palazzol/demon/targets/bin/asteroid_tether/asteroid_tether.rst

                              1 ;****************************************************************
                              2 ; This file is auto-generated by ddmake from asteroid_tether.toml
                              3 ; *** DO NOT EDIT ***
                              4 ;****************************************************************
                              5 
                              6 ; Start of chip memory mapping
                     F800     7 STRTADD = 0xf800
                              8 
                              9 ; 2K ROM
                     0800    10 ROMSIZE = 0x0800
                             11 
                             12 ; Start of ram, needs 7 bytes starting here
                             13 ; On the 6502, you can usually you can count on there being RAM in page 0
                     0000    14 RAMSTRT = 0x0000
                             15 
                             16 ; Start of stack, needs some memory below this address
                             17 ; On the 6502, this is in page 1, so this actually represents
                             18 ; address 0x0100+SSTACK
                     00FF    19 SSTACK = 0x00ff
                             20 
                             21 ; delay factor
                     0180    22 BIGDEL = 0x0180
                             23 
                             24         .include "../core/dd.def"
                              1 
                     0000     2 ROMEND  .equ    STRTADD+ROMSIZE
                              3 
                              4 
                             25         .include "../core/6502.def"
                              1 ; Same for all 6502s
                     FFFA     2 VECTORS .equ    0xfffa      ; location of Vector table
                             26 
                             27 ;------- region1  -----------------------------------------------
                             28 
                             29         .bank   region1 (base=STRTADD, size=VECTORS-STRTADD)
                             30         .area   region1 (ABS, BANK=region1)
                             31 
                             32 ;
                             33 ;       START CODE
                             34 ;
   F800                      35 START:
   F800 78            [ 2]   36         sei              ; Disable interrupts - we don't handle them
   F801 A2 FF         [ 2]   37         ldx     #SSTACK  ; set up the stack
   F803 9A            [ 2]   38         txs
   F804 D8            [ 2]   39         cld              ; No Decimal
                             40 ;       YOUR CODE CAN GO HERE
   F805 4C 08 F8      [ 3]   41         jmp     INIT
                             42 
                             43         .include "../core/6502_main.asm"
                              1 ;;;;;;;;;;;;;;;;;;;;;;;;;;;;;;;;;;;;;;;;;;;;;;;;;;;;;;;;;;;;;;;;;;;;;;;;;;;
                              2 ; RAM Variables 
                              3 ;;;;;;;;;;;;;;;;;;;;;;;;;;;;;;;;;;;;;;;;;;;;;;;;;;;;;;;;;;;;;;;;;;;;;;;;;;;
                              4 
                     0000     5 OUTBUF  .equ    RAMSTRT         ;buffer for output states
                     0001     6 B       .equ    RAMSTRT+0x01    ;general purpose
                     0002     7 C       .equ    RAMSTRT+0x02    ;general purpose
                     0003     8 CMDBUF0 .equ    RAMSTRT+0x03    ;command buffer
                     0004     9 CMDBUF1 .equ    RAMSTRT+0x04    ;command buffer
                     0005    10 CMDBUF2 .equ    RAMSTRT+0x05    ;command buffer
                     0006    11 CMDBUF3 .equ    RAMSTRT+0x06    ;command buffer
                             12 
                             13 ; I2C ADDRESSING
                     0011    14 I2CRADR .equ    0x11        ; I2C read address  - I2C address 0x08
                     0010    15 I2CWADR .equ    0x10        ; I2C write address - I2C address 0x08
                             16 
   F808                      17 INIT:
   F808 A9 00         [ 2]   18         lda     #0x00
   F80A 85 00         [ 3]   19         sta     OUTBUF
                             20 
                             21 ; Main routine
   F80C                      22 MAIN:
   F80C 20 0B F9      [ 6]   23         jsr     EVERY
   F80F 20 C6 F8      [ 6]   24         jsr     POLL
   F812 B0 F8         [ 4]   25         bcs     MAIN
   F814 A9 01         [ 2]   26         lda     #BIGDEL>>8
   F816 85 01         [ 3]   27         sta     B
   F818 A9 80         [ 2]   28         lda     #BIGDEL%256
   F81A 85 02         [ 3]   29         sta     C
   F81C                      30 MLOOP:
   F81C A5 02         [ 3]   31         lda     C
   F81E F0 05         [ 4]   32         beq     DECBOTH
   F820 C6 02         [ 5]   33         dec     C
   F822 4C 1C F8      [ 3]   34         jmp     MLOOP
   F825                      35 DECBOTH:
   F825 A5 01         [ 3]   36         lda     B
   F827 F0 E3         [ 4]   37         beq     MAIN
   F829 C6 02         [ 5]   38         dec     C
   F82B C6 01         [ 5]   39         dec     B
   F82D 4C 1C F8      [ 3]   40         jmp     MLOOP
                             41 
                             42 ; Delay for half a bit time
   F830 60            [ 6]   43 I2CDLY: rts             ; TBD - this is plenty?
                             44 
                             45 ; I2C Start Condition
   F831                      46 I2CSTART:
   F831 20 30 F9      [ 6]   47         jsr    CLRSDA      
   F834 20 19 F9      [ 6]   48         jsr    CLRSCL
   F837 60            [ 6]   49         rts
                             50 
                             51 ; I2C Stop Condition
                             52 ; Uses HL
                             53 ; Destroys A
   F838                      54 I2CSTOP:
   F838 20 30 F9      [ 6]   55         jsr    CLRSDA
   F83B 20 0C F9      [ 6]   56         jsr    SETSCL
   F83E 20 23 F9      [ 6]   57         jsr    SETSDA
   F841 60            [ 6]   58         rts
                             59         
   F842                      60 I2CRBIT:
   F842 20 23 F9      [ 6]   61         jsr     SETSDA
   F845 20 0C F9      [ 6]   62         jsr     SETSCL
   F848 20 3D F9      [ 6]   63         jsr     READSDA ; sets/clears carry flag
   F84B 20 19 F9      [ 6]   64         jsr     CLRSCL
   F84E 60            [ 6]   65         rts             ; carry flag still good here
                             66 
   F84F                      67 I2CWBIT:
   F84F 90 06         [ 4]   68         bcc     DOCLR
   F851 20 23 F9      [ 6]   69         jsr     SETSDA
   F854 4C 5A F8      [ 3]   70         jmp     AHEAD
   F857                      71 DOCLR:
   F857 20 30 F9      [ 6]   72         jsr     CLRSDA
   F85A                      73 AHEAD:
   F85A 20 0C F9      [ 6]   74         jsr     SETSCL
   F85D 20 19 F9      [ 6]   75         jsr     CLRSCL
   F860 60            [ 6]   76         rts
                             77         
   F861                      78 I2CWBYTE:
   F861 48            [ 3]   79         pha
   F862 A9 08         [ 2]   80         lda     #0x08
   F864 85 01         [ 3]   81         sta     B
   F866 68            [ 4]   82         pla
   F867                      83 ILOOP:
   F867 2A            [ 2]   84         rol
   F868 48            [ 3]   85         pha
   F869 20 4F F8      [ 6]   86         jsr     I2CWBIT
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
   F8F1 A5 05         [ 3]  164         lda     CMDBUF2
   F8F3 85 01         [ 3]  165         sta     B
   F8F5 A5 04         [ 3]  166         lda     CMDBUF1
   F8F7 85 02         [ 3]  167         sta     C
   F8F9 60            [ 6]  168         rts
                            169         
   F8FA                     170 SRESP:
   F8FA 20 B5 F8      [ 6]  171         jsr    I2CSRESP
   F8FD                     172 RHERE:
   F8FD 38            [ 2]  173         sec
   F8FE 60            [ 6]  174         rts
   F8FF                     175 REMCALL:
   F8FF A9 F7         [ 2]  176         lda     #>(START-1)
   F901 48            [ 3]  177         pha
   F902 A9 FF         [ 2]  178         lda     #<(START-1)
   F904 48            [ 3]  179         pha
   F905 20 F1 F8      [ 6]  180         jsr     LOADBC
   F908 6C 01 00      [ 5]  181         jmp     [B]
                            182         
                            183 ;;;;;;;;;;
                            184 
                            185 
                             44 ;
                             45 ;       EVERY CODE
                             46 ;
   F90B                      47 EVERY:
                             48 ;       YOUR CODE CAN GO HERE
   F90B 60            [ 6]   49         rts
                             50 
                             51         .include "../io/asteroid-tether.asm"
                              1 
                              2 ; SCL  - WRITE 0x3200, bit0 (0x01) 2 player start lamp - active low only because led is wired to +5V
                              3 ; DOUT - WRITE 0x3200, bit1 (0x02) 1 player start lamp - active low only because led is wired to +5V
                              4 ; DIN  - READ  0x2405, bit7 (0x80) thrust button - inverted on input
                              5 
                     2800     6 DIP7    .equ    0x2800  ;bit0 = DIP switch 7
                     3200     7 LEDS    .equ    0x3200  ;bit0 = 2 player start lamp
                              8                         ;bit1 = 1 player start lamp
                              9         
                     0000    10 LEDBUF  .equ    OUTBUF  ;buffer for lamps
                             11 
   F90C A5 00         [ 3]   12 SETSCL: lda     LEDBUF
   F90E 09 01         [ 2]   13         ora     #0x01
   F910 85 00         [ 3]   14         sta     LEDBUF
   F912 8D 00 32      [ 4]   15         sta     LEDS
   F915 20 30 F8      [ 6]   16         jsr     I2CDLY
   F918 60            [ 6]   17         rts
                             18 
   F919 A5 00         [ 3]   19 CLRSCL: lda     LEDBUF
   F91B 29 FE         [ 2]   20         and     #0xfe
   F91D 85 00         [ 3]   21         sta     LEDBUF
   F91F 8D 00 32      [ 4]   22         sta     LEDS
   F922 60            [ 6]   23         rts
                             24     
   F923 A5 00         [ 3]   25 SETSDA: lda     LEDBUF
   F925 29 FD         [ 2]   26         and     #0xfd
   F927 85 00         [ 3]   27         sta     LEDBUF
   F929 8D 00 32      [ 4]   28         sta     LEDS
   F92C 20 30 F8      [ 6]   29         jsr     I2CDLY
   F92F 60            [ 6]   30         rts
                             31 
   F930 A5 00         [ 3]   32 CLRSDA: lda     LEDBUF
   F932 09 02         [ 2]   33         ora     #0x02
   F934 85 00         [ 3]   34         sta     LEDBUF
   F936 8D 00 32      [ 4]   35         sta     LEDS
   F939 20 30 F8      [ 6]   36         jsr     I2CDLY
   F93C 60            [ 6]   37         rts
                             38 
   F93D                      39 READSDA:        
   F93D AD 00 28      [ 4]   40         lda DIP7
   F940 6A            [ 2]   41         ror         
   F941 60            [ 6]   42         rts
                             43      
                             44     
                             52 ;
                             53 ;       NMI HANDLER
                             54 ;
   F942                      55 NMI:
   F942 40            [ 6]   56         rti
                             57 
                             58 
                             59 ;------- region2  -----------------------------------------------
                             60 
                             61         .bank   region2 (base=VECTORS, size=ROMSIZE-VECTORS)
                             62         .area   region2 (ABS, BANK=region2)
                             63 
                             64         .include "../core/6502_vectors.asm"
   FFFA 42 F9                 1         .dw     NMI
   FFFC 00 F8                 2         .dw     START
   FFFE 00 F8                 3         .dw     START
                             65
