palazzol/demon/doc/DD_Presentation-VCFMW_2022.pdf

# Demon Debugger

VCF Midwest - 10-September-2022 Frank Palazzolo
Evan Allen

## Introduction and Questions…

? ? ? ? ? ? ? ? ?
? ? ? ? ? ? ? ? ?

## What is Demon Debugger?

## Demon Debugger an flexible, open tool, used to help repair and reverse-engineer old computers*

*computers = computers, game consoles, arcade machines, SBCs, etc.

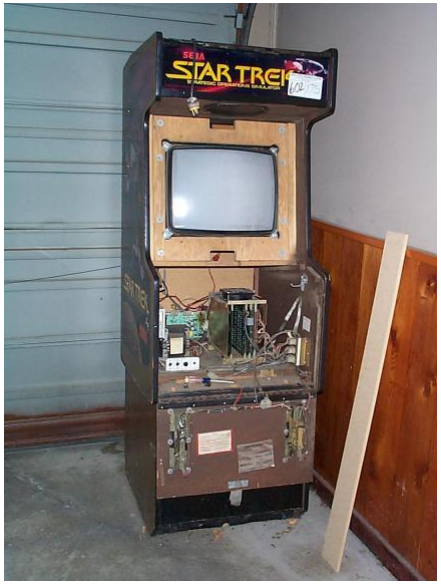
[picture p7: figure]

## Demon Debugger - 2016

Repairing a Star Trek arcade machine

Built by Sega in 1982, purchased it in 1999

Where do I start?

Initial Idea - Can I use it to debug itself?

If it can run code, and has a little RAM:

1) Run my own Z80 code on this
2) Find a few I/O Pins that I can use to make it talk to me

## Demon Debugger - Tethered mode

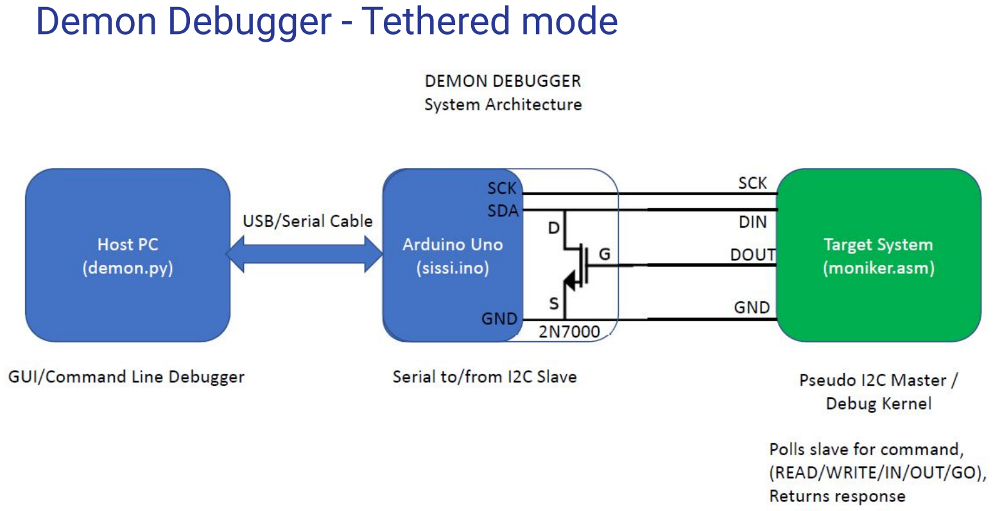
[picture p8: page 5]

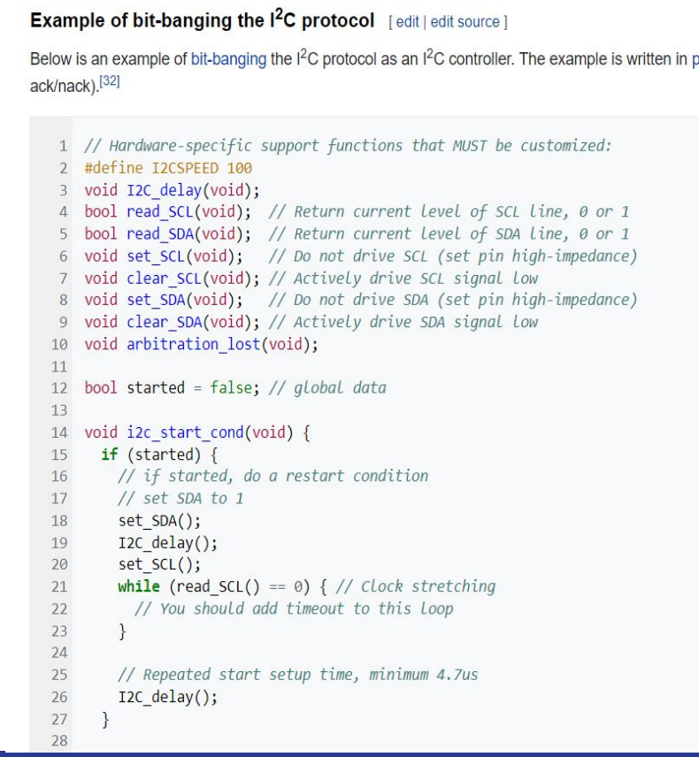
[picture p9: figure]

## Demon Debugger - 2016

Target code:

Polling loop

Bit-Bang I2C Master* for Z80

(Based on Wikipedia code)

Command Handler

Read from Address/Port

Write from Address/Port

Call and Address

## Demon Debugger - 2016

Who will I talk to? Arduino Uno

Already talks I2C!

Arduino Uno code:

Respond to Polls over I2C Slave interface

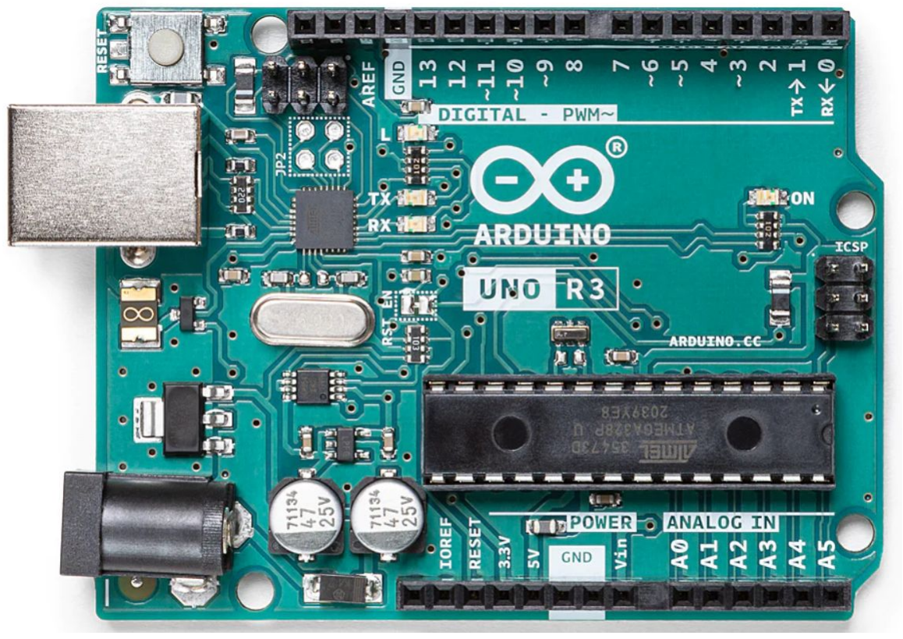
[picture p10: figure]

Respond to USB Serial commands from PC

PC code:

Command-line interface written in Python

## Demon Debugger - 2016

Small Hardware Issue - I2C is a bidirectional bus.

I didn’t want target to require bidirectional pin on the target

Use a single transistor to adapt:

Real I2C (2-wires + ground)

“Pseudo-I2C” (3-wires + ground)

## Star Trek Repair successful!

…but it took a while

Demon Debugger was key in all steps, along with information from MAME

Repaired each board in the card cage

Repaired Vector Display

Z80 code is fairly easy to adapt to another platform, I/O and RAM

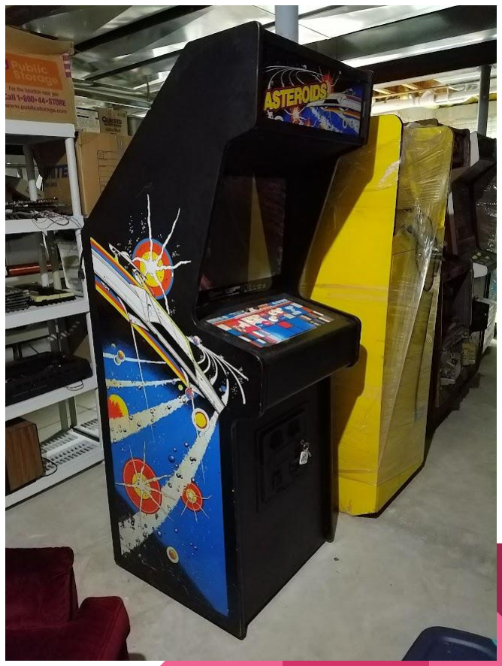
[picture p11: figure]

## Atari Asteroids Repair

Ported the target code from Z80 to 6502

(subset of functions, no Port I/O)

No issues, worked like a champ!

Note: 6502 code is even easier to adapt to other hardware, uses page zero RAM

Now Demon Debugger is Multi-platform!

## A 3rd Platform?

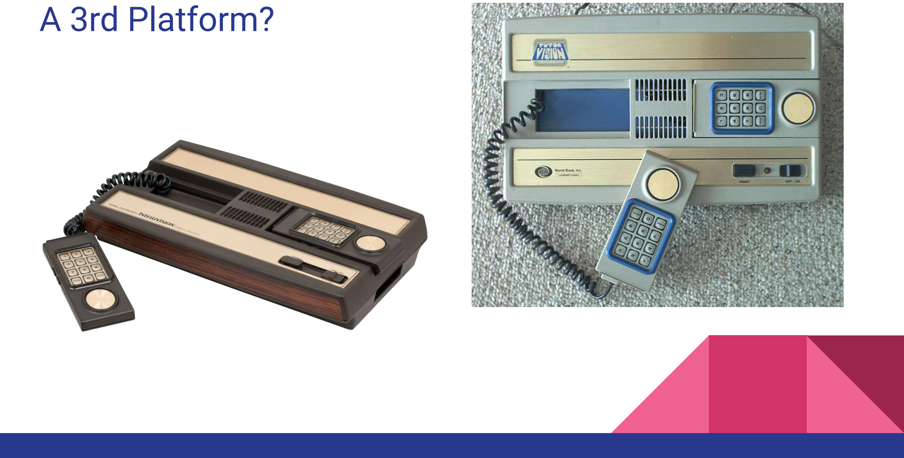
[picture p12: page 11]

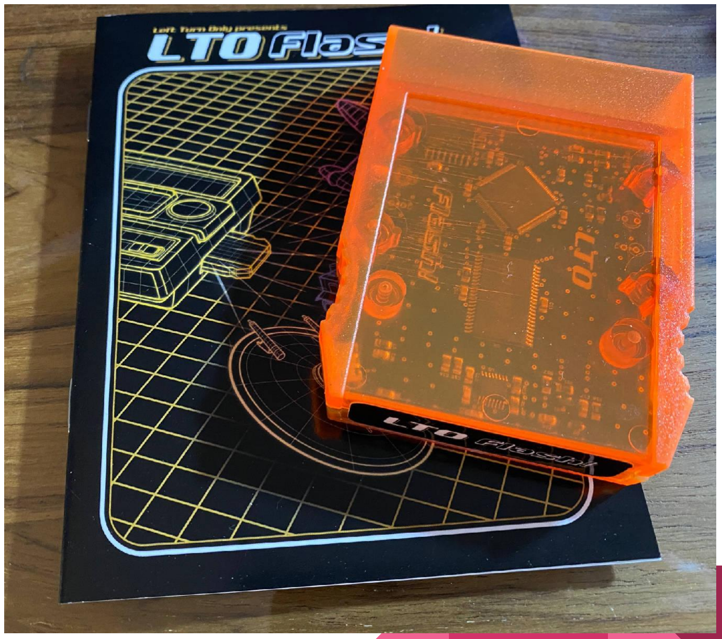
[picture p13: figure]

## Tutorvision BIOS dump

How can I dump the Tutorvision BIOS?

CPU is a GI CP1610

LTO-Flash cart can run code, and it has a serial port.

Run the serial part of Demon Debugger on the cart

Did this, and the BIOS was dumped

3rd platform - sort of!

## What if we just don’t have the I/O?

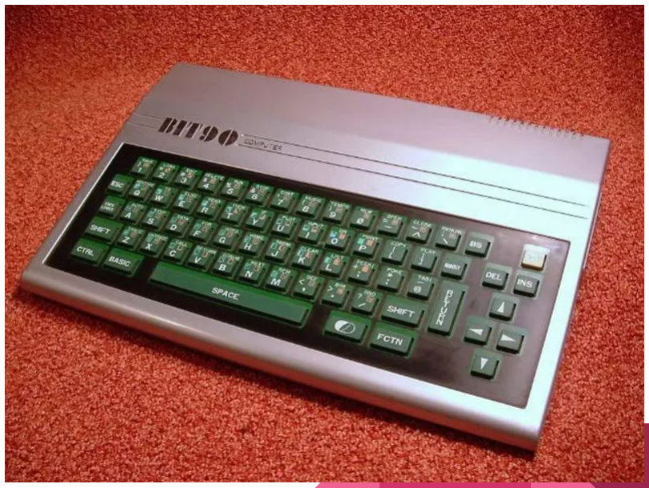
[picture p14: figure]

Pristine, rare computer!

ROMs to dump on the inside

Cartridge port is compatible with the ColecoVision (Z80)

## What if we just don’t have the I/O?

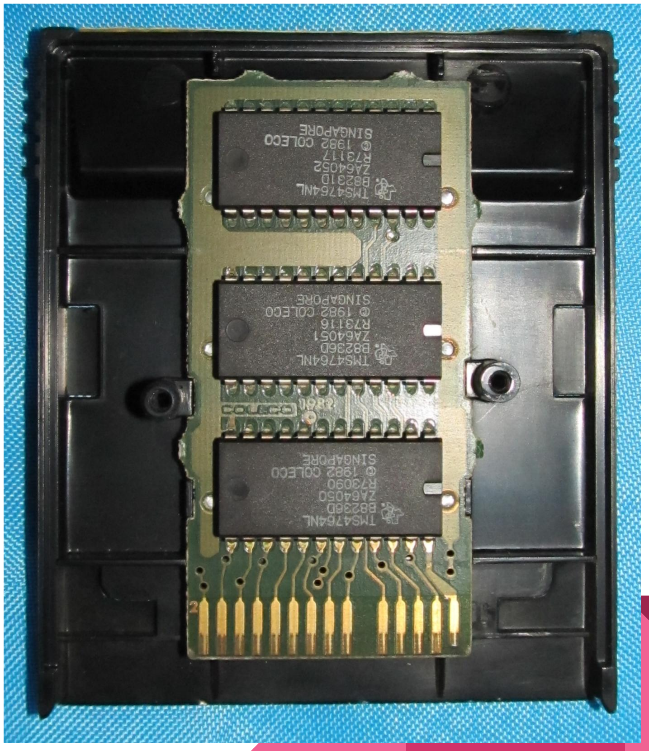
[picture p15: figure]

(ColecoVision Cart has 3 ROMs)

We can put Demon Debugger target code into ROM1.

Idea:

What if we turn read accesses to ROM2 and ROM3 into read and write signals to the Arduino?

## Birth of Demon Debugger - Memory Mapped I/O

Reads to ROM1 will read DD code

Reads to ROM2 will read D0

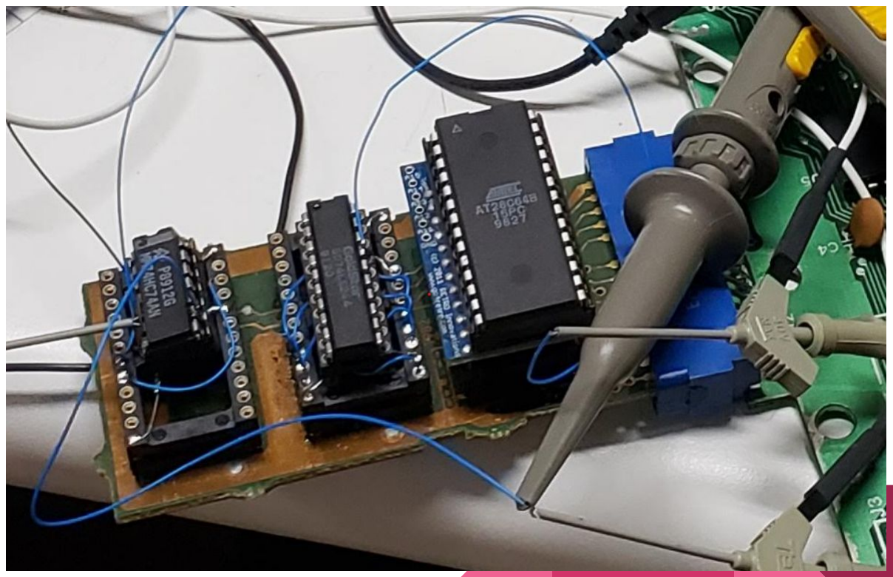
[picture p16: figure]

Reads to ROM3 will write A1/A0 | PIC of cart here

Uses only a few chips, works great!

## Birth of Demon Debugger - Memory Mapped I/O

New way of using Demon Debugger

Replace a 2K memory region

Compatible with a 2716 ROM

Code plus memory mapped I/O

Replace the ROM, I/O is included!

Note:

I/O in middle, can you guess why?

Memory Map:

0x000-0x1ff Available for Code

0x200-0x3ff Available for Code

0x400-0x5ff I/O Region

0x400-0x5ff Available for Code

## Birth of Demon Debugger - Memory Mapped I/O

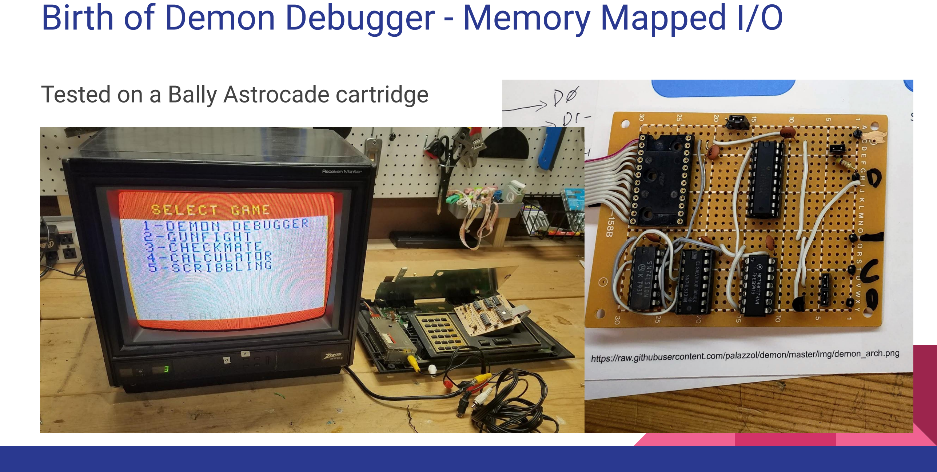
[picture p17: page 17]

Tested on a Bally Astrocade cartridge

## Time for a PCB! Rev A

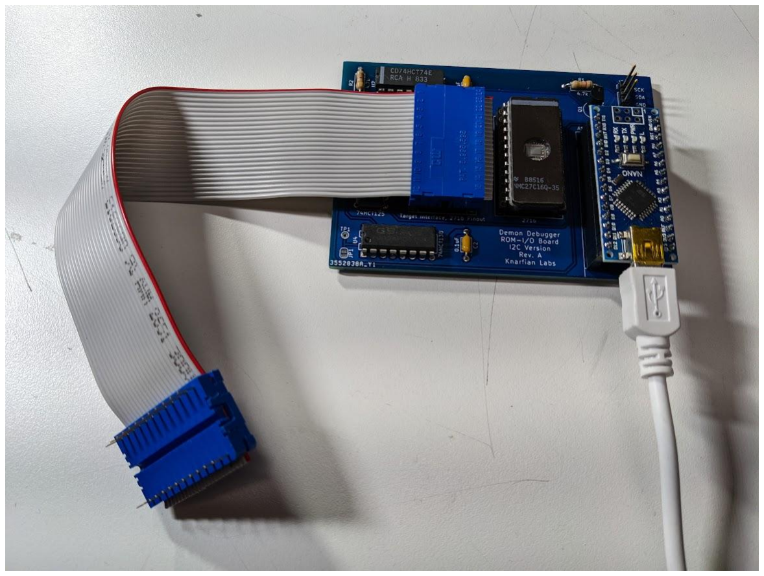
[picture p18: figure]

Memory Map I/O

Onboard EPROM chip

Cable to 2716 standard ROM header

Can still support tethered mode

What could go wrong?

## Delayed edges, and other horrors

It doesn’t work consistently! It needs one mod for a Z80, another for 6502!

The issue is using is the hack of using Address Lines as Data to write to the Arduino. Address Lines are not easy to grab based on ~OE and ~CE states.

Solution:

We already have a memory on board. When you want to write, just read from the I/O write location, but also let the memory provide the data to write.

Now all platforms can to IO exactly the same way!

## Demon Debugger Hardware - Rev. B?

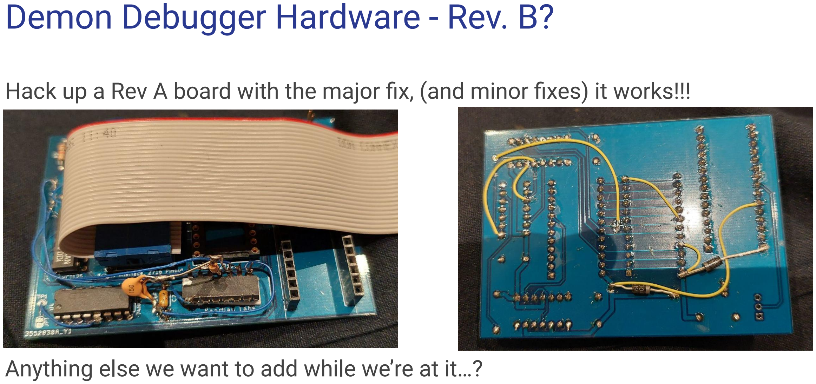
[picture p19: page 20]

Hack up a Rev A board with the major fix, (and minor fixes) it works!!!

Anything else we want to add while we’re at it…?

## Demon Debugger - Reprogrammability

We now can use an onboard 2716 EPROM, or have a 28C16 (2K Flash chip)

But to use it, it still requires a chip programmer.

More convenient to expand the design to allow for reprogramming the Flash!

Rev C:

Add I/O expander to handle programming

## Demon Debugger Hardware - Rev. C

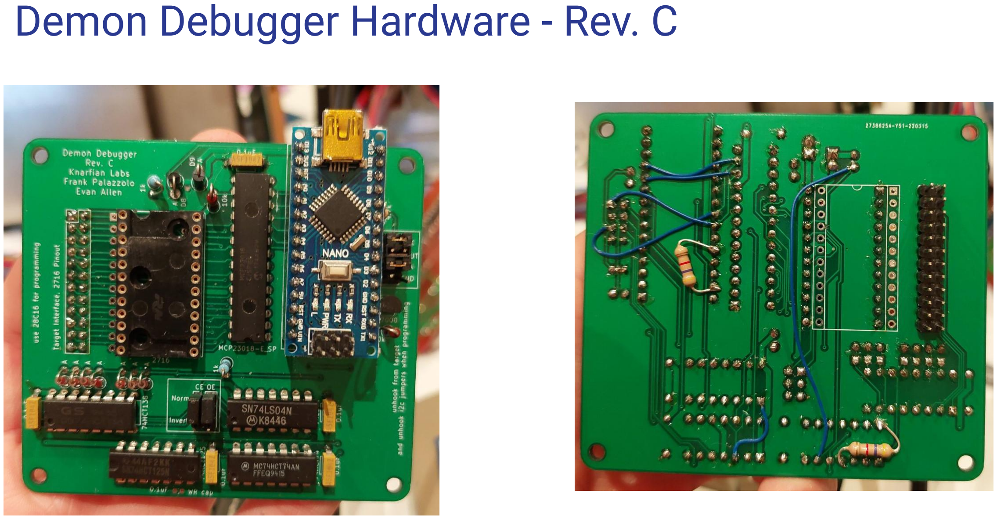
[picture p20: page 22]

## Demon Debugger 2022 - Rev D

More fixes

Need 2 separate I2C interfaces

Other bug fixes

New Features

We decide to shrink and move the I/O regions

Maximize useable code region

Support tiny roms

## Demon Debugger 2022 - Rev D

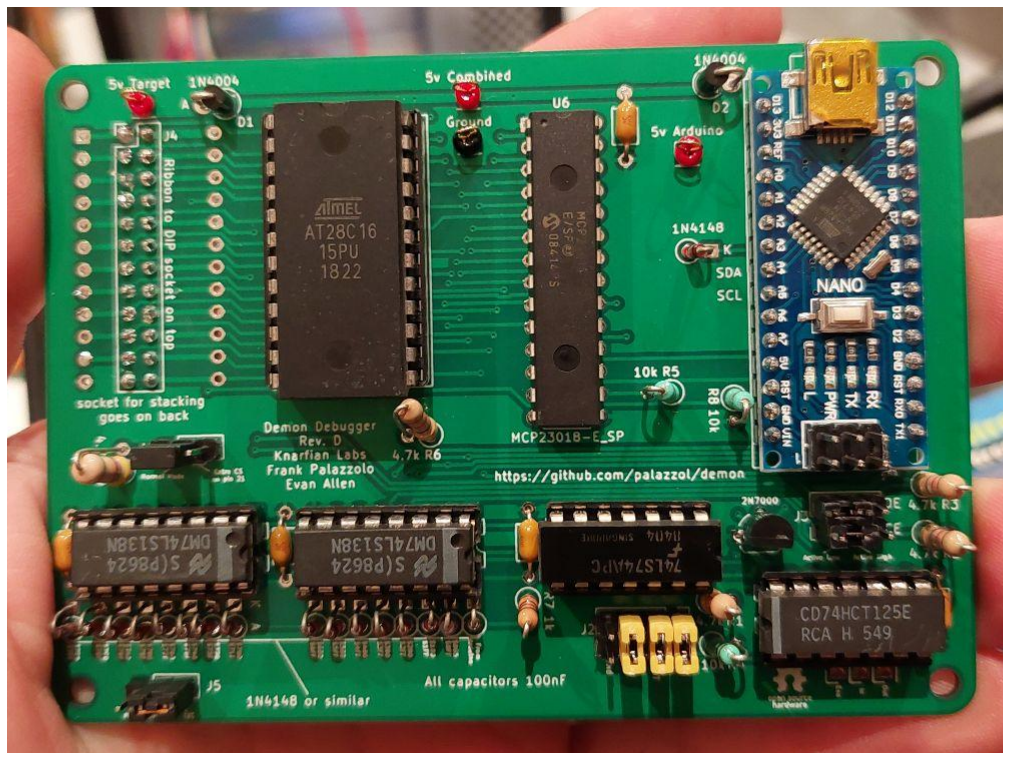
[picture p21: figure]

Memory Map

0x000-0x7bf Available

0x7a0-0c7bf Read Arduino

0x7c0-0x7df Write Arduino

0x7e0-0x7ff Available

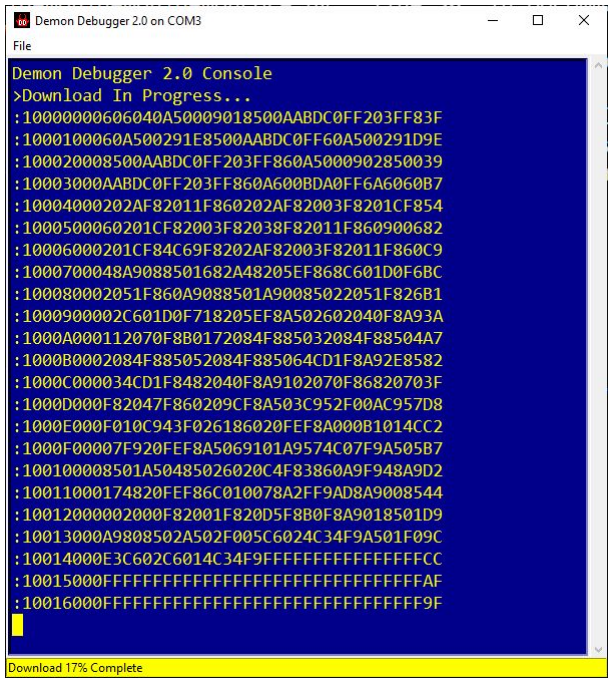
[picture p22: figure]

## Demon Debugger GUI

New software necessary for reflashing, might as well start on a GUI now

GUI uses Python + Tk (built in)

Current Status:

GUI upload/download code to flash

CLI program still used for the rest

2.0 Release - Make the GUI fully functional

## Demon Debugger - Python API

Can be used for automated data acquisition, for example

Target reads and writes along with other acquisitions:

Rigol Scope used for Data Acquisition

Rigol Scope screen caps

Logic Analyzer

RGB color sensor

## Demon Debugger - Software structure

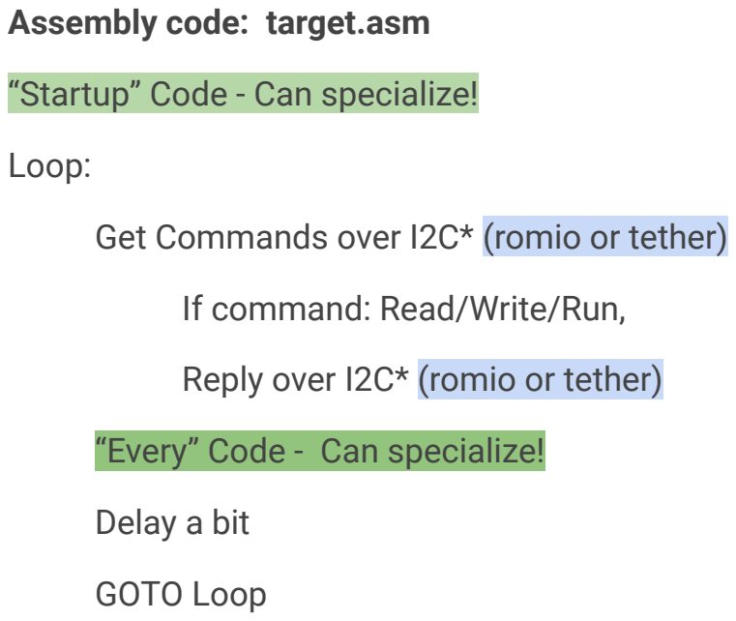
[picture p23: figure]
Assembly code: target.asm; “Startup” Code - Can specialize!; Loop:; If command: Read/Write/Run,; Reply over I2C* (romio or tether); “Every” Code -; Can specialize!; Delay a bit; GOTO Loop

Get Commands over I2C* (romio or tether)

Arduino code: I2C Slave / Serial converter

If Serial command:

buffer it for I2C

If I2C command:

Read buffer, send serial if needed

Send buffer back over I2C

Python CLI or GUI:

UI - Command/Response

over Serial

## Demon Debugger - Building a Target

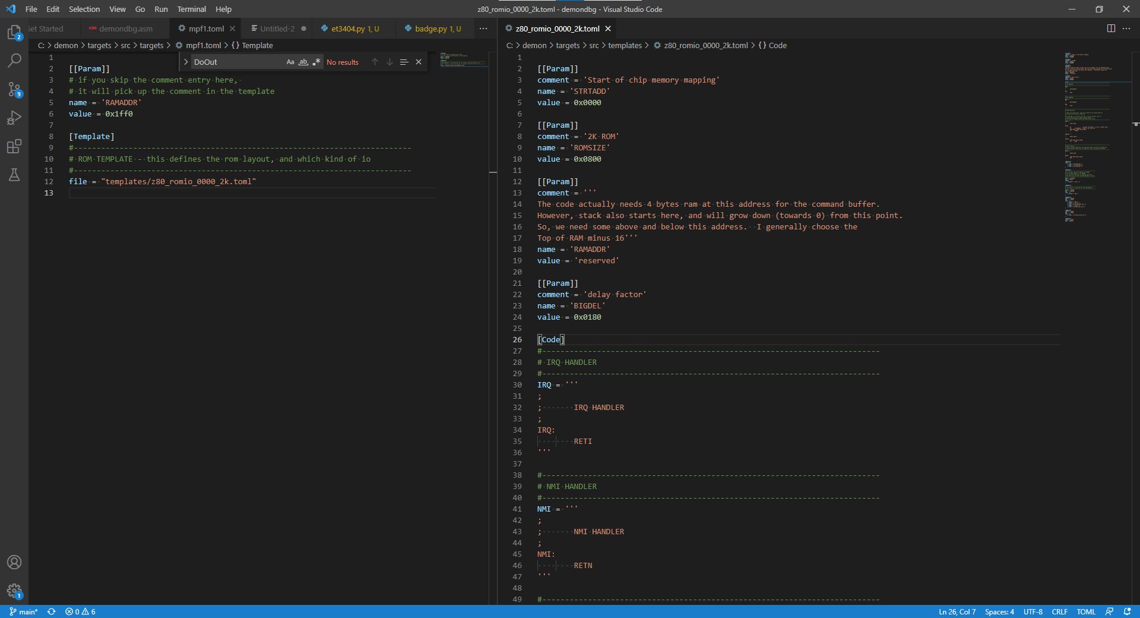
[picture p24: figure]

Python and TOML files

Look like old school .INI files, meant for human editing

ddmake.py tools generates new targets from templates and config files

## Demon Debugger - Rev D. Hardware Features

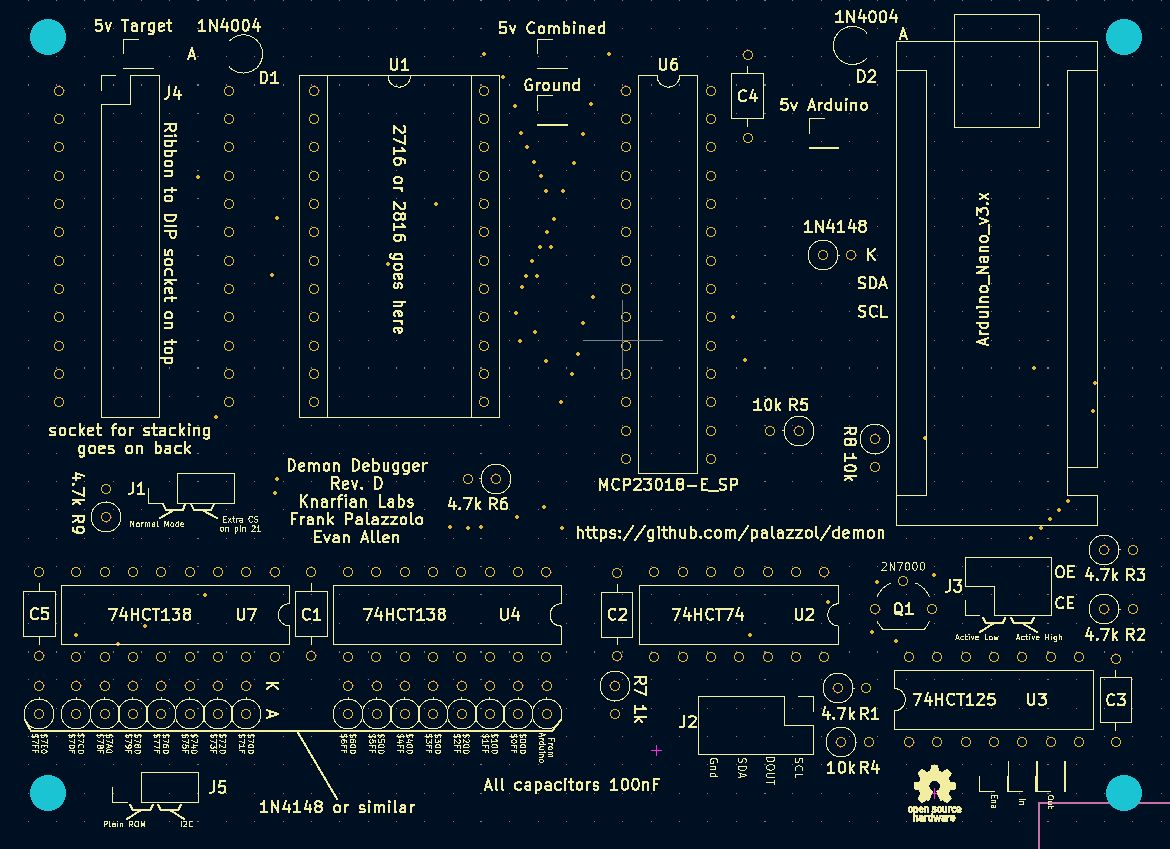
[picture p25: figure]

## Demon Debugger - Rev D. Hardware Features

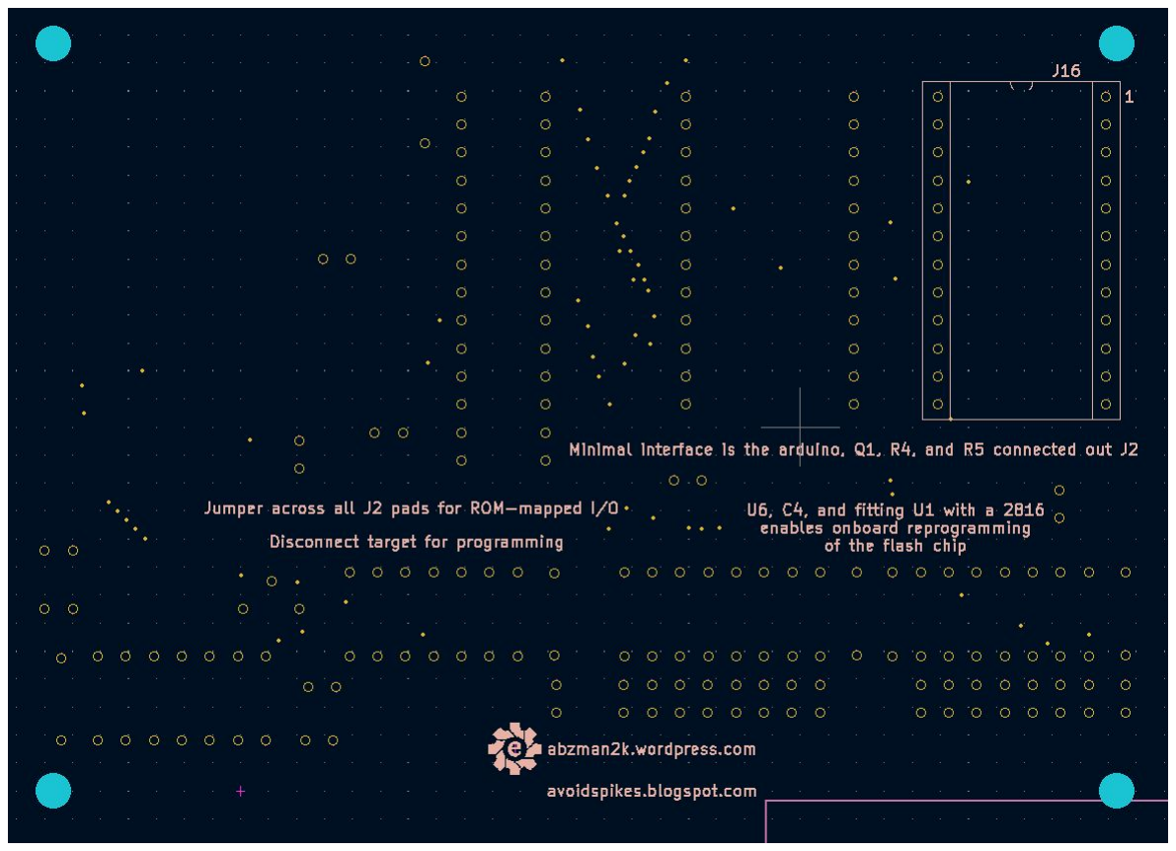
[picture p26: figure]

## Demon Debugger - The Future

More CPUs - 8085, 8080, RCA1802, TMS9900, CP1610

More Platforms - Test and deploy on Windows, Linux and Mac

Keep improving system for Target code

More GUI - Better GUI - Memory windows?

More Users!

Rev. E? - Raspberry Pi Pico?

## Thank You!

### Repo link - github.com/palazzol/demon

### Evan Allen - abzman2k.wordpress.com

### Frank Palazzolo - avoidspikes.blogspot.com
