palazzol/demon/targets/bin/starshp1/starshp1.rst

                              1 ;****************************************************************
                              2 ; This file is auto-generated by ddmake from starshp1.toml
                              3 ; *** DO NOT EDIT ***
                              4 ;****************************************************************
                              5 
                              6 ; Start of chip memory mapping
                     F800     7 STRTADD = 0xf800
                              8 
                              9 ; 2K ROM
                     0800    10 ROMSIZE = 0x0800
                             11 
                             12 ; Start of ram, needs 7 bytes starting here
                             13 ; On the 6502, you can usually you can count on there being RAM in page 0
                     0000    14 RAMSTRT = 0x0000
                             15 
                             16 ; Start of stack, needs some memory below this address
                             17 ; On the 6502, this is in page 1, so this actually represents
                             18 ; address 0x0100+SSTACK
                     00FF    19 SSTACK = 0x00ff
                             20 
                             21 ; delay factor
                     0180    22 BIGDEL = 0x0180
                             23 
                             24         .include "../core/dd.def"
                              1 
                     0000     2 ROMEND  .equ    STRTADD+ROMSIZE
                              3 
                              4 
                             25         .include "../core/6502.def"
                              1 ; Same for all 6502s
                     FFFA     2 VECTORS .equ    0xfffa      ; location of Vector table
                             26         .include "../io/romio.def"
                              1 ; For Demon Debugger Hardware - Rev D 
                              2 
                     FFA0     3 IOREGR   .equ   STRTADD+0x07a0    ;reserved region for IO READ
                     FFC0     4 IOREGW   .equ   STRTADD+0x07c0    ;reserved region for IO WRITE
                              5 
                     FFA0     6 IOADD    .equ   IOREGR            ;start of region
                     FFE0     7 IOEND    .equ   STRTADD+0x07e0    ;end of region
                             27 
                             28 ;------- region1  -----------------------------------------------
                             29 
                             30         .bank   region1 (base=STRTADD, size=IOADD-STRTADD)
                             31         .area   region1 (ABS, BANK=region1)
                             32 
                             33 ;
                             34 ;       START CODE
                             35 ;
   F800                      36 START:
   F800 78            [ 2]   37         sei              ; Disable interrupts - we don't handle them
   F801 A2 FF         [ 2]   38         ldx     #SSTACK  ; set up the stack
   F803 9A            [ 2]   39         txs
   F804 D8            [ 2]   40         cld              ; No Decimal
                             41 ;       YOUR CODE CAN GO HERE
   F805 4C 08 F8      [ 3]   42         jmp     INIT
                             43 
                             44         .include "../core/6502_main.asm"
                              1 ;;;;;;;;;;;;;;;;;;;;;;;;;;;;;;;;;;;;;;;;;;;;;;;;;;;;;;;;;;;;;;;;;;;;;;;;;;;
                              2 ; RAM Variables 
                              3 ;;;;;;;;;;;;;;;;;;;;;;;;;;;;;;;;;;;;;;;;;;;;;;;;;;;;;;;;;;;;;;;;;;;;;;;;;;;
                              4 
                     0000     5 OUTBUF  .equ    RAMSTRT         ;buffer for output states
                     0001     6 B       .equ    RAMSTRT+0x01    ;general purpose
                     0002     7 C       .equ    RAMSTRT+0x02    ;general purpose
                     0003     8 CMDBUF0 .equ    RAMSTRT+0x03    ;command buffer
                     0004     9 CMDBUF1 .equ    RAMSTRT+0x04    ;command buffer
                     0005    10 CMDBUF2 .equ    RAMSTRT+0x05    ;command buffer
                     0006    11 CMDBUF3 .equ    RAMSTRT+0x06    ;command buffer
                             12 
                             13 ; I2C ADDRESSING
                     0011    14 I2CRADR .equ    0x11        ; I2C read address  - I2C address 0x08
                     0010    15 I2CWADR .equ    0x10        ; I2C write address - I2C address 0x08
                             16 
   F808                      17 INIT:
   F808 A9 00         [ 2]   18         lda     #0x00
   F80A 85 00         [ 3]   19         sta     OUTBUF
                             20 
                             21 ; Main routine
   F80C                      22 MAIN:
   F80C 20 0B F9      [ 6]   23         jsr     EVERY
   F80F 20 C6 F8      [ 6]   24         jsr     POLL
   F812 B0 F8         [ 4]   25         bcs     MAIN
   F814 A9 01         [ 2]   26         lda     #BIGDEL>>8
   F816 85 01         [ 3]   27         sta     B
   F818 A9 80         [ 2]   28         lda     #BIGDEL%256
   F81A 85 02         [ 3]   29         sta     C
   F81C                      30 MLOOP:
   F81C A5 02         [ 3]   31         lda     C
   F81E F0 05         [ 4]   32         beq     DECBOTH
   F820 C6 02         [ 5]   33         dec     C
   F822 4C 1C F8      [ 3]   34         jmp     MLOOP
   F825                      35 DECBOTH:
   F825 A5 01         [ 3]   36         lda     B
   F827 F0 E3         [ 4]   37         beq     MAIN
   F829 C6 02         [ 5]   38         dec     C
   F82B C6 01         [ 5]   39         dec     B
   F82D 4C 1C F8      [ 3]   40         jmp     MLOOP
                             41 
                             42 ; Delay for half a bit time
   F830 60            [ 6]   43 I2CDLY: rts             ; TBD - this is plenty?
                             44 
                             45 ; I2C Start Condition
   F831                      46 I2CSTART:
   F831 20 79 F9      [ 6]   47         jsr    CLRSDA      
   F834 20 60 F9      [ 6]   48         jsr    CLRSCL
   F837 60            [ 6]   49         rts
                             50 
                             51 ; I2C Stop Condition
                             52 ; Uses HL
                             53 ; Destroys A
   F838                      54 I2CSTOP:
   F838 20 79 F9      [ 6]   55         jsr    CLRSDA
   F83B 20 52 F9      [ 6]   56         jsr    SETSCL
   F83E 20 6B F9      [ 6]   57         jsr    SETSDA
   F841 60            [ 6]   58         rts
                             59         
   F842                      60 I2CRBIT:
   F842 20 6B F9      [ 6]   61         jsr     SETSDA
   F845 20 52 F9      [ 6]   62         jsr     SETSCL
   F848 20 87 F9      [ 6]   63         jsr     READSDA ; sets/clears carry flag
   F84B 20 60 F9      [ 6]   64         jsr     CLRSCL
   F84E 60            [ 6]   65         rts             ; carry flag still good here
                             66 
   F84F                      67 I2CWBIT:
   F84F 90 06         [ 4]   68         bcc     DOCLR
   F851 20 6B F9      [ 6]   69         jsr     SETSDA
   F854 4C 5A F8      [ 3]   70         jmp     AHEAD
   F857                      71 DOCLR:
   F857 20 79 F9      [ 6]   72         jsr     CLRSDA
   F85A                      73 AHEAD:
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
   F948 8D 00 CC      [ 4]   71         sta     0xcc00
   F94B 8D 00 CC      [ 4]   72         sta     0xcc00
   F94E 8D 06 DC      [ 4]   73         sta     0xdc06
   F951 60            [ 6]   74         rts
                             75 
                             76 
                             77         .include "../io/6502_romio.asm"
   F952 A5 00         [ 3]    1 SETSCL: lda     OUTBUF
   F954 09 01         [ 2]    2         ora     #0x01
   F956 85 00         [ 3]    3         sta     OUTBUF
   F958 AA            [ 2]    4         tax
   F959 BD C0 FF      [ 5]    5         lda     IOREGW,X
   F95C 20 30 F8      [ 6]    6         jsr     I2CDLY
   F95F 60            [ 6]    7         rts
                              8 
   F960 A5 00         [ 3]    9 CLRSCL: lda     OUTBUF
   F962 29 1E         [ 2]   10         and     #0x1e
   F964 85 00         [ 3]   11         sta     OUTBUF
   F966 AA            [ 2]   12         tax
   F967 BD C0 FF      [ 5]   13         lda     IOREGW,X
   F96A 60            [ 6]   14         rts
                             15 
   F96B A5 00         [ 3]   16 SETSDA: lda     OUTBUF
   F96D 29 1D         [ 2]   17         and     #0x1d
   F96F 85 00         [ 3]   18         sta     OUTBUF
   F971 AA            [ 2]   19         tax
   F972 BD C0 FF      [ 5]   20         lda     IOREGW,X
   F975 20 30 F8      [ 6]   21         jsr     I2CDLY
   F978 60            [ 6]   22         rts
                             23 
   F979 A5 00         [ 3]   24 CLRSDA: lda     OUTBUF
   F97B 09 02         [ 2]   25         ora     #0x02
   F97D 85 00         [ 3]   26         sta     OUTBUF
   F97F AA            [ 2]   27         tax
   F980 BD C0 FF      [ 5]   28         lda     IOREGW,X
   F983 20 30 F8      [ 6]   29         jsr     I2CDLY
   F986 60            [ 6]   30         rts
                             31 
   F987                      32 READSDA:
   F987 A6 00         [ 3]   33         ldx     OUTBUF
   F989 BD A0 FF      [ 5]   34         lda     IOREGR,X
   F98C 6A            [ 2]   35         ror
   F98D 60            [ 6]   36         rts
                             37                              
                             78 ;
                             79 ;       NMI HANDLER
                             80 ;
   F98E                      81 NMI:
   F98E 40            [ 6]   82         rti
                             83 
                             84 
                             85 ;------- region2  -----------------------------------------------
                             86 
                             87         .bank   region2 (base=IOADD, size=IOEND-IOADD)
                             88         .area   region2 (ABS, BANK=region2)
                             89 
                             90         .include "../io/romio_table.asm"
                              1 
                              2 ; 
                              3 ; For Demon Debugger Hardware - Rev D 
                              4 ;
                              5 ; In earlier hardware designs, I tried to capture the address bus bits on a 
                              6 ; read cycle, to use to write to the Arduino.  But it turns out it is impossible
                              7 ; to know exactly when to sample these address bits across all platforms, designs, and 
                              8 ; clock speeds
                              9 ;
                             10 ; The solution I came up with was to make sure the data bus contains the same information
                             11 ; as the lower address bus during these read cycles, so that I can sample the data bus just like the 
                             12 ; CPU would.
                             13 ;
                             14 ; This block of memory, starting at 0x07c0, is filled with consecutive integers.
                             15 ; When the CPU reads from a location, the data bus matches the lower bits of the address bus.  
                             16 ; And the data bus read by the CPU is also written to the Arduino.
                             17 ; 
                             18 ; Note: Currently, only the bottom two bits are used, but reserving the memory
                             19 ; this way insures that up to 5 bits could be used 
                             20 ; 
                             21         ; ROMIO READ Area - reserved
   FFA0 FF FF FF FF FF FF    22         .DB     0xff,0xff,0xff,0xff,0xff,0xff,0xff,0xff,0xff,0xff,0xff,0xff,0xff,0xff,0xff,0xff
        FF FF FF FF FF FF
        FF FF FF FF
   FFB0 FF FF FF FF FF FF    23         .DB     0xff,0xff,0xff,0xff,0xff,0xff,0xff,0xff,0xff,0xff,0xff,0xff,0xff,0xff,0xff,0xff
        FF FF FF FF FF FF
        FF FF FF FF
                             24 
                             25         ; ROMIO WRITE Area - data is used
   FFC0 00 01 02 03 04 05    26         .DB     0x00,0x01,0x02,0x03,0x04,0x05,0x06,0x07,0x08,0x09,0x0a,0x0b,0x0c,0x0d,0x0e,0x0f
        06 07 08 09 0A 0B
        0C 0D 0E 0F
   FFD0 10 11 12 13 14 15    27         .DB     0x10,0x11,0x12,0x13,0x14,0x15,0x16,0x17,0x18,0x19,0x1a,0x1b,0x1c,0x1d,0x1e,0x1f
        16 17 18 19 1A 1B
        1C 1D 1E 1F
                             28 
                             91 
                             92 ;------- region3  -----------------------------------------------
                             93 
                             94         .bank   region3 (base=VECTORS, size=ROMSIZE-VECTORS)
                             95         .area   region3 (ABS, BANK=region3)
                             96 
                             97         .include "../core/6502_vectors.asm"
   FFFA 8E F9                 1         .dw     NMI
   FFFC 00 F8                 2         .dw     START
   FFFE 00 F8                 3         .dw     START
                             98
