palazzol/demon/targets/bin/startrek/startrek.rst

                              1 ;****************************************************************
                              2 ; This file is auto-generated by ddmake from startrek.toml
                              3 ; *** DO NOT EDIT ***
                              4 ;****************************************************************
                              5 
                              6 ; Start of chip memory mapping
                     0000     7 STRTADD = 0x0000
                              8 
                              9 ; 2K ROM
                     0800    10 ROMSIZE = 0x0800
                             11 
                             12 ; The code actually needs 4 bytes ram at this address for the command buffer.
                             13 ; However, stack also starts here, and will grow down (towards 0) from this point.
                             14 ; So, we need some above and below this address.  I generally choose the
                             15 ; Top of RAM minus 16
                     CFF0    16 RAMADDR = 0xcff0
                             17 
                             18 ; delay factor
                     0180    19 BIGDEL = 0x0180
                             20 
                             21         .include "../core/dd.def"
                              1 
                     0800     2 ROMEND  .equ    STRTADD+ROMSIZE
                              3 
                              4 
                             22         .include "../core/z80.def"
                              1 ; Same for all Z80s
                     0038     2 IRQADD  .equ    0x0038      ; location of IRQ handler
                     0066     3 NMIADD  .equ    0x0066      ; location of NMI handler
                             23         .include "../io/romio.def"
                              1 ; For Demon Debugger Hardware - Rev D 
                              2 
                     07A0     3 IOREGR   .equ   STRTADD+0x07a0    ;reserved region for IO READ
                     07C0     4 IOREGW   .equ   STRTADD+0x07c0    ;reserved region for IO WRITE
                              5 
                     07A0     6 IOADD    .equ   IOREGR            ;start of region
                     07E0     7 IOEND    .equ   STRTADD+0x07e0    ;end of region
                             24 
                             25 ;------- region1  -----------------------------------------------
                             26 
                             27         .bank   region1 (base=STRTADD, size=IRQADD-STRTADD)
                             28         .area   region1 (ABS, BANK=region1)
                             29 
                             30 ;
                             31 ;       START CODE
                             32 ;
   0000                      33 START:
   0000 F3            [ 4]   34         DI                  ; Disable interrupts - we don't handle them
   0001 31 F0 CF      [10]   35         LD      SP,RAMADDR  ; have to set valid SP
                             36 ;       YOUR SMALL CODE CAN GO HERE
   0004 C3 68 00      [10]   37         JP      START2
                             38 
                             39 
                             40 ;------- region2  -----------------------------------------------
                             41 
                             42         .bank   region2 (base=IRQADD, size=NMIADD-IRQADD)
                             43         .area   region2 (ABS, BANK=region2)
                             44 
                             45 ;
                             46 ;       IRQ HANDLER
                             47 ;
   0038                      48 IRQ:
   0038 ED 4D         [14]   49         RETI
                             50 
                             51 
                             52 ;------- region3  -----------------------------------------------
                             53 
                             54         .bank   region3 (base=NMIADD, size=IOADD-NMIADD)
                             55         .area   region3 (ABS, BANK=region3)
                             56 
                             57 ;
                             58 ;       NMI HANDLER
                             59 ;
   0066                      60 NMI:
   0066 ED 45         [14]   61         RETN
                             62 
                             63 ;
                             64 ;       START CODE 2
                             65 ;
   0068                      66 START2:
   0068 3E 81         [ 7]   67         LD      A,0x81
   006A 21 00 E0      [10]   68         LD      HL,0xE000
   006D 77            [ 7]   69         LD      (HL),A      ; blank the screen
   006E C3 71 00      [10]   70         JP      INIT
                             71 
                             72         .include "../core/z80_main.asm"
                              1 ; I2C ADDRESSING
                     0011     2 I2CRADR .equ    0x11        ; I2C read address  - I2C address 0x08
                     0010     3 I2CWADR .equ    0x10        ; I2C write address - I2C address 0x08
                              4 
                              5 ;;;;;;;;;;;;;;;;;;;;;;;;;;;;;;;;;;;;;;;;;;;;;;;;;;;;;;;;;;;;;;;;;;;;;;;;;;;
                              6 ; RAM Variables	
                              7 ;;;;;;;;;;;;;;;;;;;;;;;;;;;;;;;;;;;;;;;;;;;;;;;;;;;;;;;;;;;;;;;;;;;;;;;;;;;
                              8 
                     CFF0     9 CMDBUF  .equ    RAMADDR     ; Need only 4 bytes of ram for command buffer
                             10 
   0071                      11 INIT:
   0071 DD 21 F0 CF   [14]   12         LD      IX,CMDBUF   ; Easy to index command buffer
   0075 16 00         [ 7]   13         LD      D,#0x00     ; initialize D to prevent index overflow
                             14 
                             15 ; Main routine
   0077                      16 MAIN:
   0077 CD 7D 01      [17]   17         CALL    EVERY
   007A CD 20 01      [17]   18         CALL    POLL
   007D DA 77 00      [10]   19         JP      C,MAIN
                             20         
   0080 01 80 01      [10]   21         LD      BC,BIGDEL
   0083                      22 DLOOP:
   0083 0B            [ 6]   23         DEC     BC
   0084 79            [ 4]   24         LD      A,C
   0085 B0            [ 4]   25         OR      B
   0086 C2 83 00      [10]   26         JP      NZ,DLOOP
   0089 C3 77 00      [10]   27         JP      MAIN
                             28 
                             29 ; Delay for half a bit time
   008C                      30 I2CDELAY:
   008C C9            [10]   31         RET     ; This is plenty
                             32 
                             33 ; I2C Start Condition
                             34 ; Uses HL
                             35 ; Destroys A
   008D                      36 I2CSTART:
   008D CD AB 01      [17]   37         CALL    CLRSDA      
   0090 CD 8E 01      [17]   38         CALL    CLRSCL
   0093 C9            [10]   39         RET
                             40 
                             41 ; I2C Stop Condition
                             42 ; Uses HL
                             43 ; Destroys A
   0094                      44 I2CSTOP:
   0094 CD AB 01      [17]   45         CALL    CLRSDA
   0097 CD 7E 01      [17]   46         CALL    SETSCL
   009A CD 9B 01      [17]   47         CALL    SETSDA
   009D C9            [10]   48         RET
                             49 
                             50 ; I2C Read Bit routine
                             51 ; Returns bit in carry blag
                             52 ; Destroys A
   009E                      53 I2CRBIT:
   009E CD 9B 01      [17]   54         CALL    SETSDA
   00A1 CD 7E 01      [17]   55         CALL    SETSCL
   00A4 CD BB 01      [17]   56         CALL    READSDA
   00A7 F5            [11]   57         PUSH    AF          ; save carry flag
   00A8 CD 8E 01      [17]   58         CALL    CLRSCL
   00AB F1            [10]   59         POP     AF          ; rv in carry flag
   00AC C9            [10]   60         RET
                             61 
                             62 ; I2C Write Bit routine
                             63 ; Takes carry flag
                             64 ; Destroys A
   00AD                      65 I2CWBIT:
   00AD 30 05         [12]   66         JR      NC,DOCLR
   00AF CD 9B 01      [17]   67         CALL    SETSDA
   00B2 18 03         [12]   68         JR      AHEAD
   00B4                      69 DOCLR:
   00B4 CD AB 01      [17]   70         CALL    CLRSDA
   00B7                      71 AHEAD:
   00B7 CD 7E 01      [17]   72         CALL    SETSCL
   00BA CD 8E 01      [17]   73         CALL    CLRSCL
   00BD C9            [10]   74         RET
                             75 
                             76 ; I2C Write Byte routine
                             77 ; Takes A
                             78 ; Destroys B
                             79 ; Returns carry bit
   00BE                      80 I2CWBYTE:
   00BE 06 08         [ 7]   81         LD      B,8
   00C0                      82 ILOOP:
   00C0 C5            [11]   83         PUSH    BC          ; save B
   00C1 CB 07         [ 8]   84         RLC     A    
   00C3 F5            [11]   85         PUSH    AF          ; save A
   00C4 CD AD 00      [17]   86         CALL    I2CWBIT
   00C7 F1            [10]   87         POP     AF
   00C8 C1            [10]   88         POP     BC
   00C9 10 F5         [13]   89         DJNZ    ILOOP
   00CB CD 9E 00      [17]   90         CALL    I2CRBIT
   00CE C9            [10]   91         RET
                             92 
                             93 ; I2C Read Byte routine
                             94 ; Destroys BC
                             95 ; Returns A
   00CF                      96 I2CRBYTE:
   00CF 06 08         [ 7]   97         LD      B,8
   00D1 0E 00         [ 7]   98         LD      C,0
   00D3                      99 LOOP3:
   00D3 C5            [11]  100         PUSH    BC
   00D4 CD 9E 00      [17]  101         CALL    I2CRBIT     ; get bit in carry flag
   00D7 C1            [10]  102         POP     BC
   00D8 CB 11         [ 8]  103         RL      C           ; rotate carry into bit0 of C register
   00DA 10 F7         [13]  104         DJNZ    LOOP3
   00DC AF            [ 4]  105         XOR     A           ; clear carry flag              
   00DD C5            [11]  106         PUSH    BC
   00DE CD AD 00      [17]  107         CALL    I2CWBIT
   00E1 C1            [10]  108         POP     BC
   00E2 79            [ 4]  109         LD      A,C
   00E3 C9            [10]  110         RET
                            111 ;
                            112 
                            113 ; Read 4-byte I2C Command from device into CMDBUF
                            114 ; Uses HL
                            115 ; Destroys A,BC,HL
   00E4                     116 I2CRREQ:
   00E4 CD 8D 00      [17]  117         CALL    I2CSTART
   00E7 3E 11         [ 7]  118         LD      A,I2CRADR
   00E9 CD BE 00      [17]  119         CALL    I2CWBYTE
   00EC 38 1A         [12]  120         JR      C,SKIP
   00EE CD CF 00      [17]  121         CALL    I2CRBYTE
   00F1 DD 77 00      [19]  122         LD      (IX),A
   00F4 CD CF 00      [17]  123         CALL    I2CRBYTE
   00F7 DD 77 01      [19]  124         LD      (IX+1),A  
   00FA CD CF 00      [17]  125         CALL    I2CRBYTE
   00FD DD 77 02      [19]  126         LD      (IX+2),A
   0100 CD CF 00      [17]  127         CALL    I2CRBYTE
   0103 DD 77 03      [19]  128         LD      (IX+3),A
   0106 18 14         [12]  129         JR      ENDI2C
                            130     
   0108                     131 SKIP:                       ; If no device present, fake an idle response
   0108 3E 2E         [ 7]  132         LD      A,0x2e  ; '.'
   010A DD 77 00      [19]  133         LD      (IX),A
   010D 18 0D         [12]  134         JR      ENDI2C
                            135 
   010F                     136 I2CSRESP:
   010F F5            [11]  137         PUSH    AF
   0110 CD 8D 00      [17]  138         CALL    I2CSTART
   0113 3E 10         [ 7]  139         LD      A,I2CWADR
   0115 CD BE 00      [17]  140         CALL    I2CWBYTE
   0118 F1            [10]  141         POP     AF
   0119 CD BE 00      [17]  142         CALL    I2CWBYTE
   011C                     143 ENDI2C:
   011C CD 94 00      [17]  144         CALL    I2CSTOP
   011F C9            [10]  145         RET
                            146 ;
                            147 
                            148 ; Main Polling loop
                            149 ; Return carry flag if we got a valid command (not idle)
   0120                     150 POLL:
   0120 CD E4 00      [17]  151         CALL    I2CRREQ
   0123 DD 7E 00      [19]  152         LD      A,(IX)
   0126 FE 52         [ 7]  153         CP      0x52    ; 'R' - Read memory
   0128 28 1B         [12]  154         JR      Z,MREAD
   012A FE 57         [ 7]  155         CP      0x57    ; 'W' - Write memory
   012C 28 1D         [12]  156         JR      Z,MWRITE
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
   0191 57            [ 4]   26         LD      D,A
   0192 E5            [11]   27         PUSH    HL
   0193 26 07         [ 7]   28         LD      H,#>IOREGW
   0195 C6 C0         [ 7]   29         ADD     A,#<IOREGW 
   0197 6F            [ 4]   30         LD      L,A
   0198 7E            [ 7]   31         LD      A,(HL)
   0199 E1            [10]   32         POP     HL
   019A C9            [10]   33         RET
                             34 
                             35 ; Set the DOUT pin low
                             36 ; D is the global output buffer
                             37 ; Destroys A 
   019B                      38 SETSDA:
   019B 7A            [ 4]   39         LD      A,D
   019C E6 1D         [ 7]   40         AND     0x1D
   019E 57            [ 4]   41         LD      D,A
   019F E5            [11]   42         PUSH    HL
   01A0 26 07         [ 7]   43         LD      H,#>IOREGW
   01A2 C6 C0         [ 7]   44         ADD     A,#<IOREGW 
   01A4 6F            [ 4]   45         LD      L,A
   01A5 7E            [ 7]   46         LD      A,(HL)
   01A6 E1            [10]   47         POP     HL
   01A7 CD 8C 00      [17]   48         CALL    I2CDELAY
   01AA C9            [10]   49         RET
                             50 
                             51 ; Set the DOUT pin high
                             52 ; D is the global output buffer
                             53 ; Destroys A  
   01AB                      54 CLRSDA:
   01AB 7A            [ 4]   55         LD      A,D
   01AC F6 02         [ 7]   56         OR      0x02
   01AE 57            [ 4]   57         LD      D,A
   01AF E5            [11]   58         PUSH    HL
   01B0 26 07         [ 7]   59         LD      H,#>IOREGW
   01B2 C6 C0         [ 7]   60         ADD     A,#<IOREGW 
   01B4 6F            [ 4]   61         LD      L,A
   01B5 7E            [ 7]   62         LD      A,(HL)
   01B6 E1            [10]   63         POP     HL
   01B7 CD 8C 00      [17]   64         CALL    I2CDELAY
   01BA C9            [10]   65         RET
                             66 
                             67 ; Read the DIN pin 
                             68 ; returns bit in carry flag    
   01BB                      69 READSDA:
   01BB 7A            [ 4]   70         LD      A,D
   01BC E5            [11]   71         PUSH    HL
   01BD 26 07         [ 7]   72         LD      H,#>IOREGR
   01BF C6 A0         [ 7]   73         ADD     A,#<IOREGR
   01C1 6F            [ 4]   74         LD      L,A
   01C2 7E            [ 7]   75         LD      A,(HL)
   01C3 E1            [10]   76         POP     HL
   01C4 CB 3F         [ 8]   77         SRL     A           ;carry flag
   01C6 C9            [10]   78         RET
                             81 
                             82 ;------- region4  -----------------------------------------------
                             83 
                             84         .bank   region4 (base=IOADD, size=IOEND-IOADD)
                             85         .area   region4 (ABS, BANK=region4)
                             86 
                             87         .include "../io/romio_table.asm"
                              1 
                              2 ; 
                              3 ; For Demon Debugger Hardware - Rev D 
                              4 ;
                              5 ; In earlier hardware designs, I tried to capture the address bus bits on a 
                              6 ; read cycle, to use to write to the Arduino.  But it turns out it is impossible
                              7 ; to know exactly when to sample these address bits across all platforms, designs, and 
                              8 ; clock speeds
                              9 ;
                             10 ; The solution I came up with was to make sure the data bus contains the same information
                             11 ; as the lower address bus during these read cycles, so that I can sample the data bus just like the 
                             12 ; CPU would.
                             13 ;
                             14 ; This block of memory, starting at 0x07c0, is filled with consecutive integers.
                             15 ; When the CPU reads from a location, the data bus matches the lower bits of the address bus.  
                             16 ; And the data bus read by the CPU is also written to the Arduino.
                             17 ; 
                             18 ; Note: Currently, only the bottom two bits are used, but reserving the memory
                             19 ; this way insures that up to 5 bits could be used 
                             20 ; 
                             21         ; ROMIO READ Area - reserved
   07A0 FF FF FF FF FF FF    22         .DB     0xff,0xff,0xff,0xff,0xff,0xff,0xff,0xff,0xff,0xff,0xff,0xff,0xff,0xff,0xff,0xff
        FF FF FF FF FF FF
        FF FF FF FF
   07B0 FF FF FF FF FF FF    23         .DB     0xff,0xff,0xff,0xff,0xff,0xff,0xff,0xff,0xff,0xff,0xff,0xff,0xff,0xff,0xff,0xff
        FF FF FF FF FF FF
        FF FF FF FF
                             24 
                             25         ; ROMIO WRITE Area - data is used
   07C0 00 01 02 03 04 05    26         .DB     0x00,0x01,0x02,0x03,0x04,0x05,0x06,0x07,0x08,0x09,0x0a,0x0b,0x0c,0x0d,0x0e,0x0f
        06 07 08 09 0A 0B
        0C 0D 0E 0F
   07D0 10 11 12 13 14 15    27         .DB     0x10,0x11,0x12,0x13,0x14,0x15,0x16,0x17,0x18,0x19,0x1a,0x1b,0x1c,0x1d,0x1e,0x1f
        16 17 18 19 1A 1B
        1C 1D 1E 1F
                             28 
                             88 
                             89 ;------- region5  -----------------------------------------------
                             90 
                             91         .bank   region5 (base=IOEND, size=ROMEND-IOEND)
                             92         .area   region5 (ABS, BANK=region5)
                             93 
                             94
