palazzol/demon/img/DemonDebuggerFullAscii.png

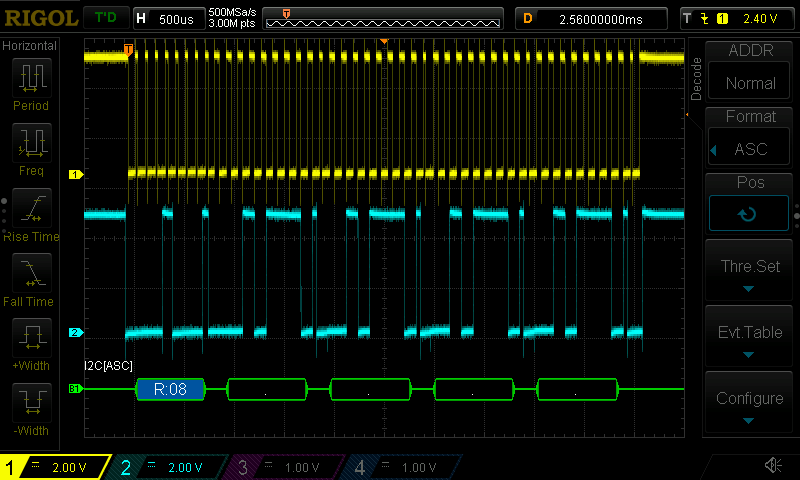
img/DemonDebuggerFullAscii.png
