palazzol/demon/targets/src/core/6811_vectors.asm

        .dw     NMI
        .dw     NMI
        .dw     NMI
        .dw     NMI
        .dw     NMI
        .dw     NMI
        .dw     NMI
        .dw     NMI
        .dw     NMI
        .dw     NMI
        .dw     NMI
        .dw     NMI
        .dw     NMI
        .dw     NMI
        .dw     NMI
        .dw     START
