palazzol/demon/targets/src/core/6809_vectors.asm

        .dw     0xFFFF   ;RESERVED
        .dw     START   ;SWI3
        .dw     START   ;SWI2
        .dw     START   ;FIRQ
        .dw     START   ;IRQ
        .dw     START   ;SWI
        .dw     NMI
        .dw     START
